Kris-Sekula/EPROM-EMU-NG/Pictures/Emulator Probe/README.MD

For DIP28 desing you can follow the YouTube video https://youtu.be/pb_EF_JVYxc

For DIP24 use the YouTube video as baseline but re-connect VCC as per desing document [Probe_Design.pdf](https://github.com/Kris-Sekula/EPROM-EMU-NG/blob/master/Probe_Design.pdf) in the main folder ... Here additonal pictures of the DIP24 probe.
