Kris-Sekula/EPROM-EMU-NG/3d-Case/Probe_lbl.PNG

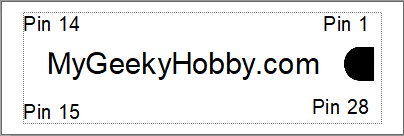
3d-Case/Probe_lbl.PNG
