Kris-Sekula/EPROM-EMU-NG/Pictures/1002_EPROM_EMU_NG_1.4.jpg

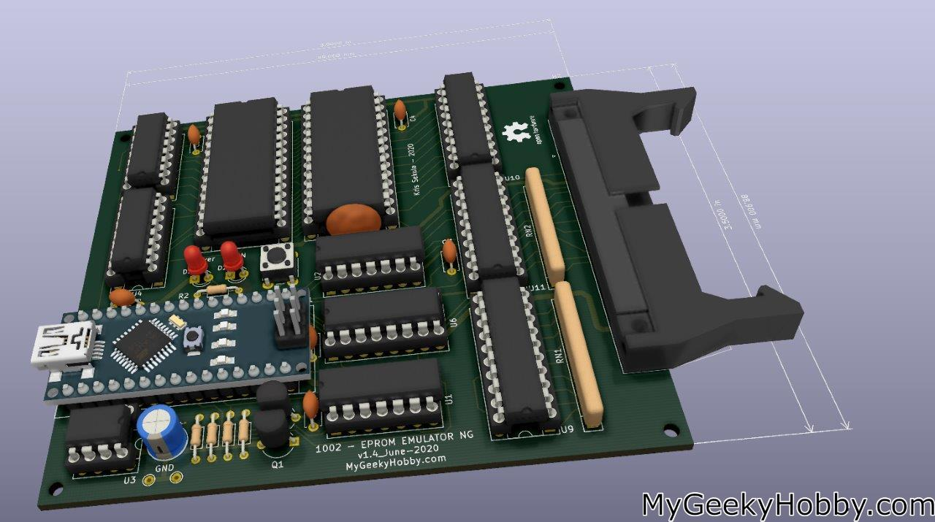
Pictures/1002_EPROM_EMU_NG_1.4.jpg
