Kris-Sekula/EPROM-EMU-NG/Pictures/EMU_1.0b_w_CA80.jpg

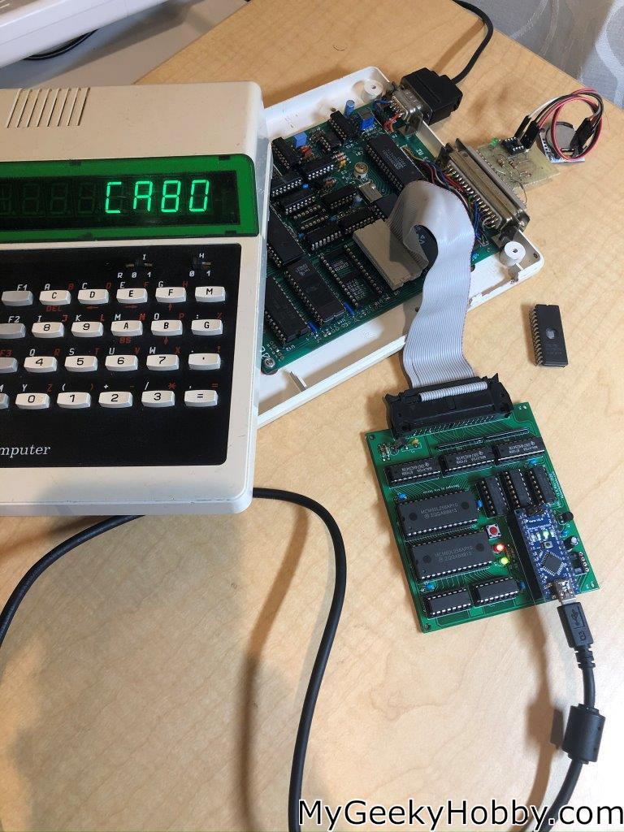
Pictures/EMU_1.0b_w_CA80.jpg
