Kris-Sekula/EPROM-EMU-NG/Pictures/EMU_1.5_ready_descr.jpg

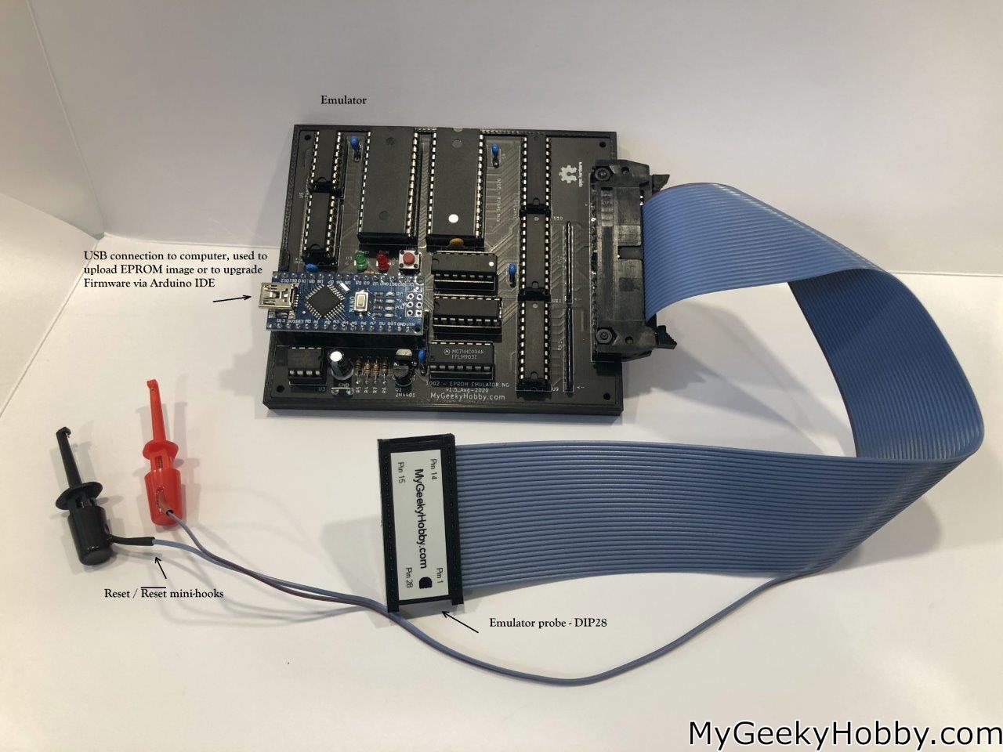
Pictures/EMU_1.5_ready_descr.jpg
