Kris-Sekula/EPROM-EMU-NG/Pictures/Emulator Probe/DIP24_1.jpg

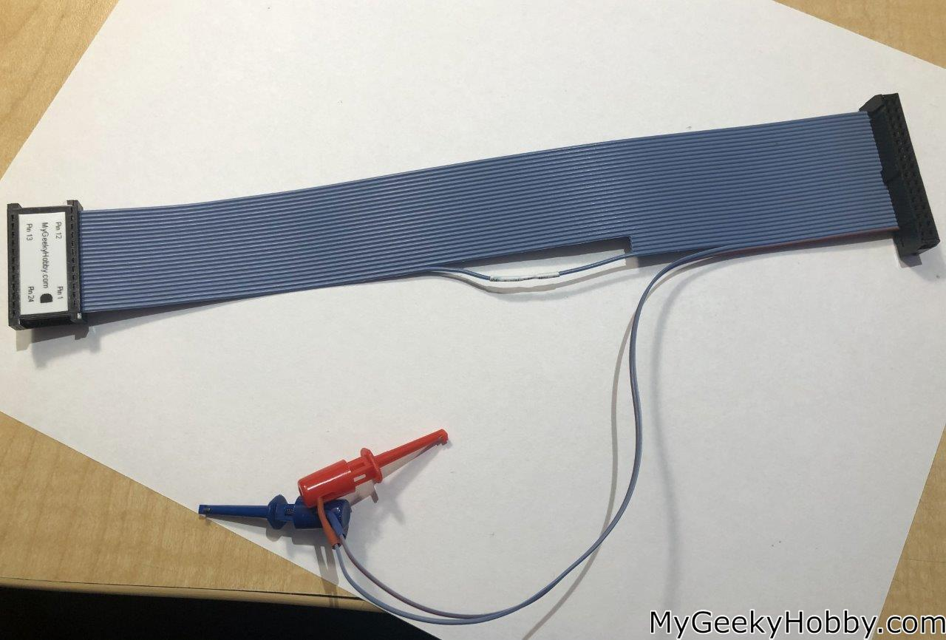
Pictures/Emulator Probe/DIP24_1.jpg
