Kris-Sekula/EPROM-EMU-NG/Pictures/Emulator Probe/DIP24_2.jpg

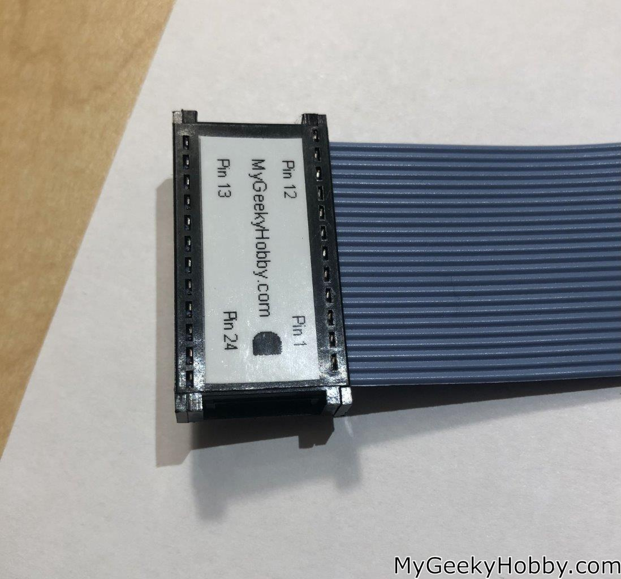
Pictures/Emulator Probe/DIP24_2.jpg
