Kris-Sekula/EPROM-EMU-NG/Pictures/Emulator Probe/DIP24_3.jpg

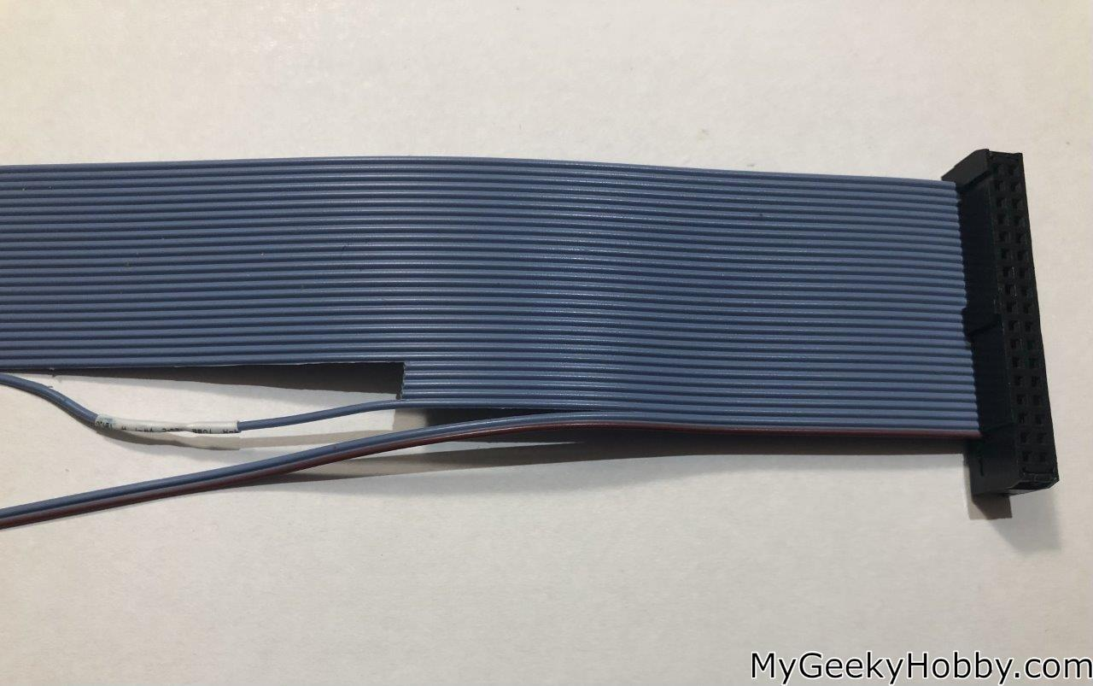
Pictures/Emulator Probe/DIP24_3.jpg
