Kris-Sekula/EPROM-EMU-NG/Pictures/Emulator Probe/DIP24_5.jpg

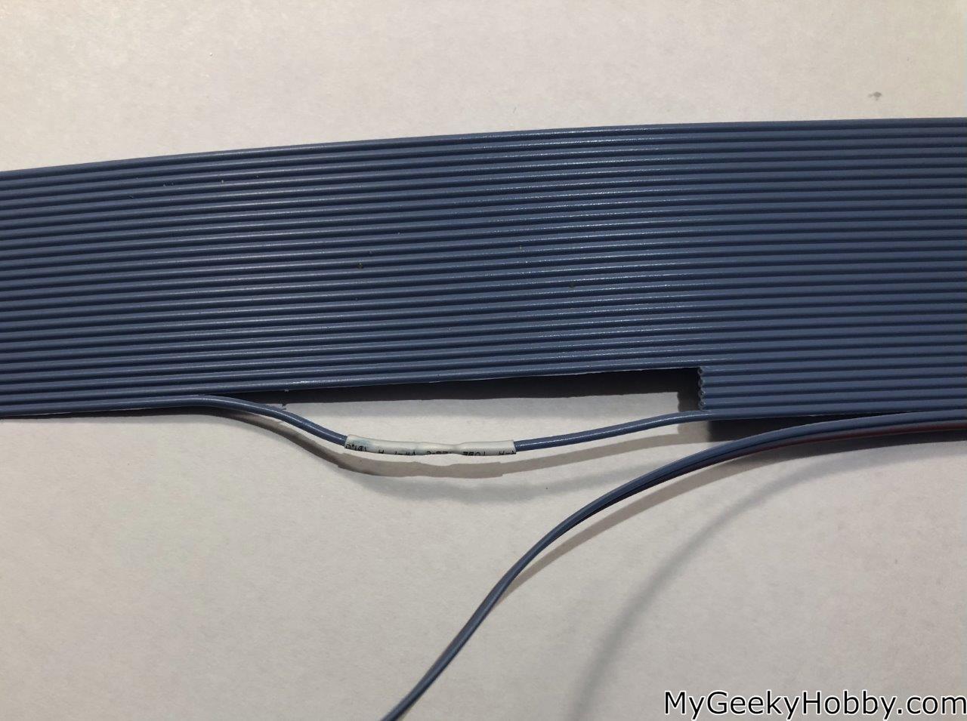
Pictures/Emulator Probe/DIP24_5.jpg
