Kris-Sekula/EPROM-EMU-NG/Pictures/EMU_1.0b_w_C64_test.jpg

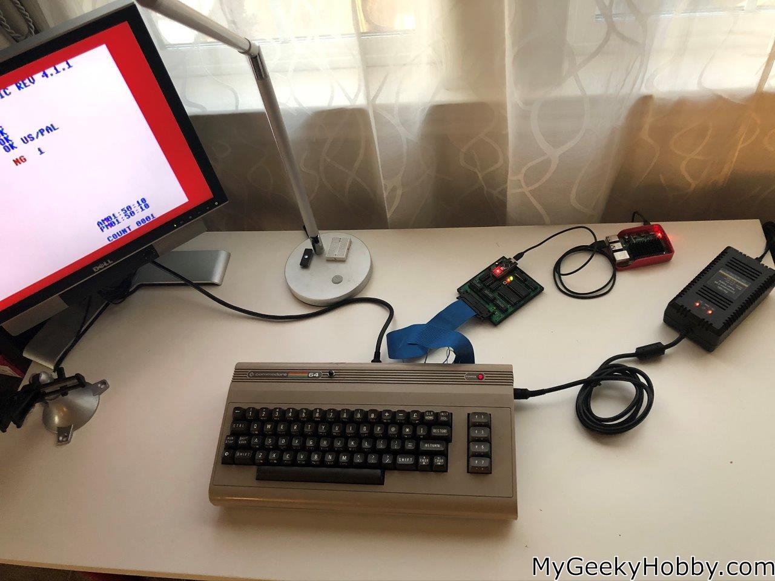
Pictures/EMU_1.0b_w_C64_test.jpg
