Kris-Sekula/EPROM-EMU-NG/1002_EPROM_EMU_NG_1.7b.pdf

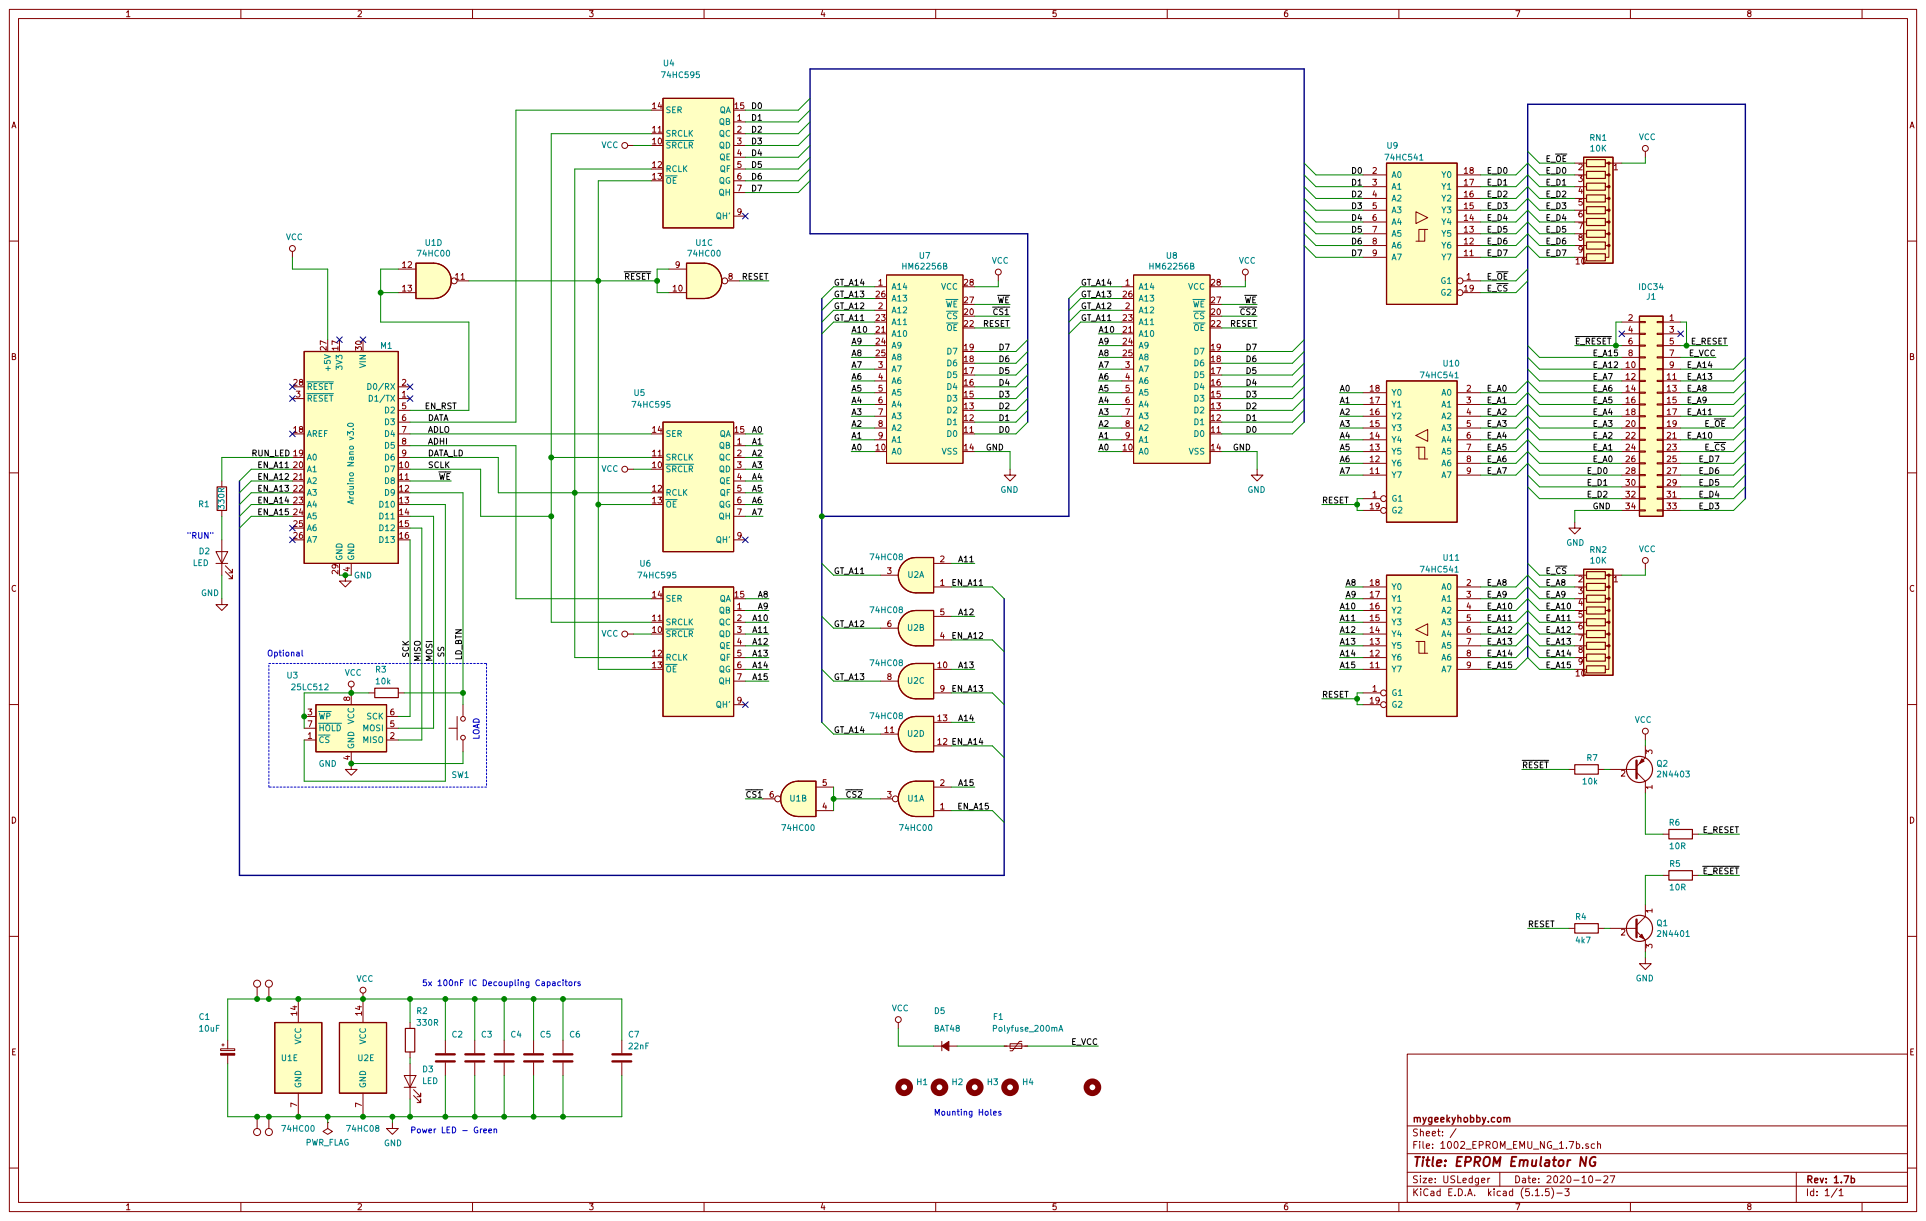
[picture p77: page 1]

Mounting Holes Power LED - Green

File: 1002_EPROM_EMU_NG_1.7b.sch Sheet: / mygeekyhobby.com

Id: 1/1 Title: EPROM Emulator NG
