Kris-Sekula/EPROM-EMU-NG/KiCad Sources/1.9/1002_EPROM_EMU_NG_1.9.pdf

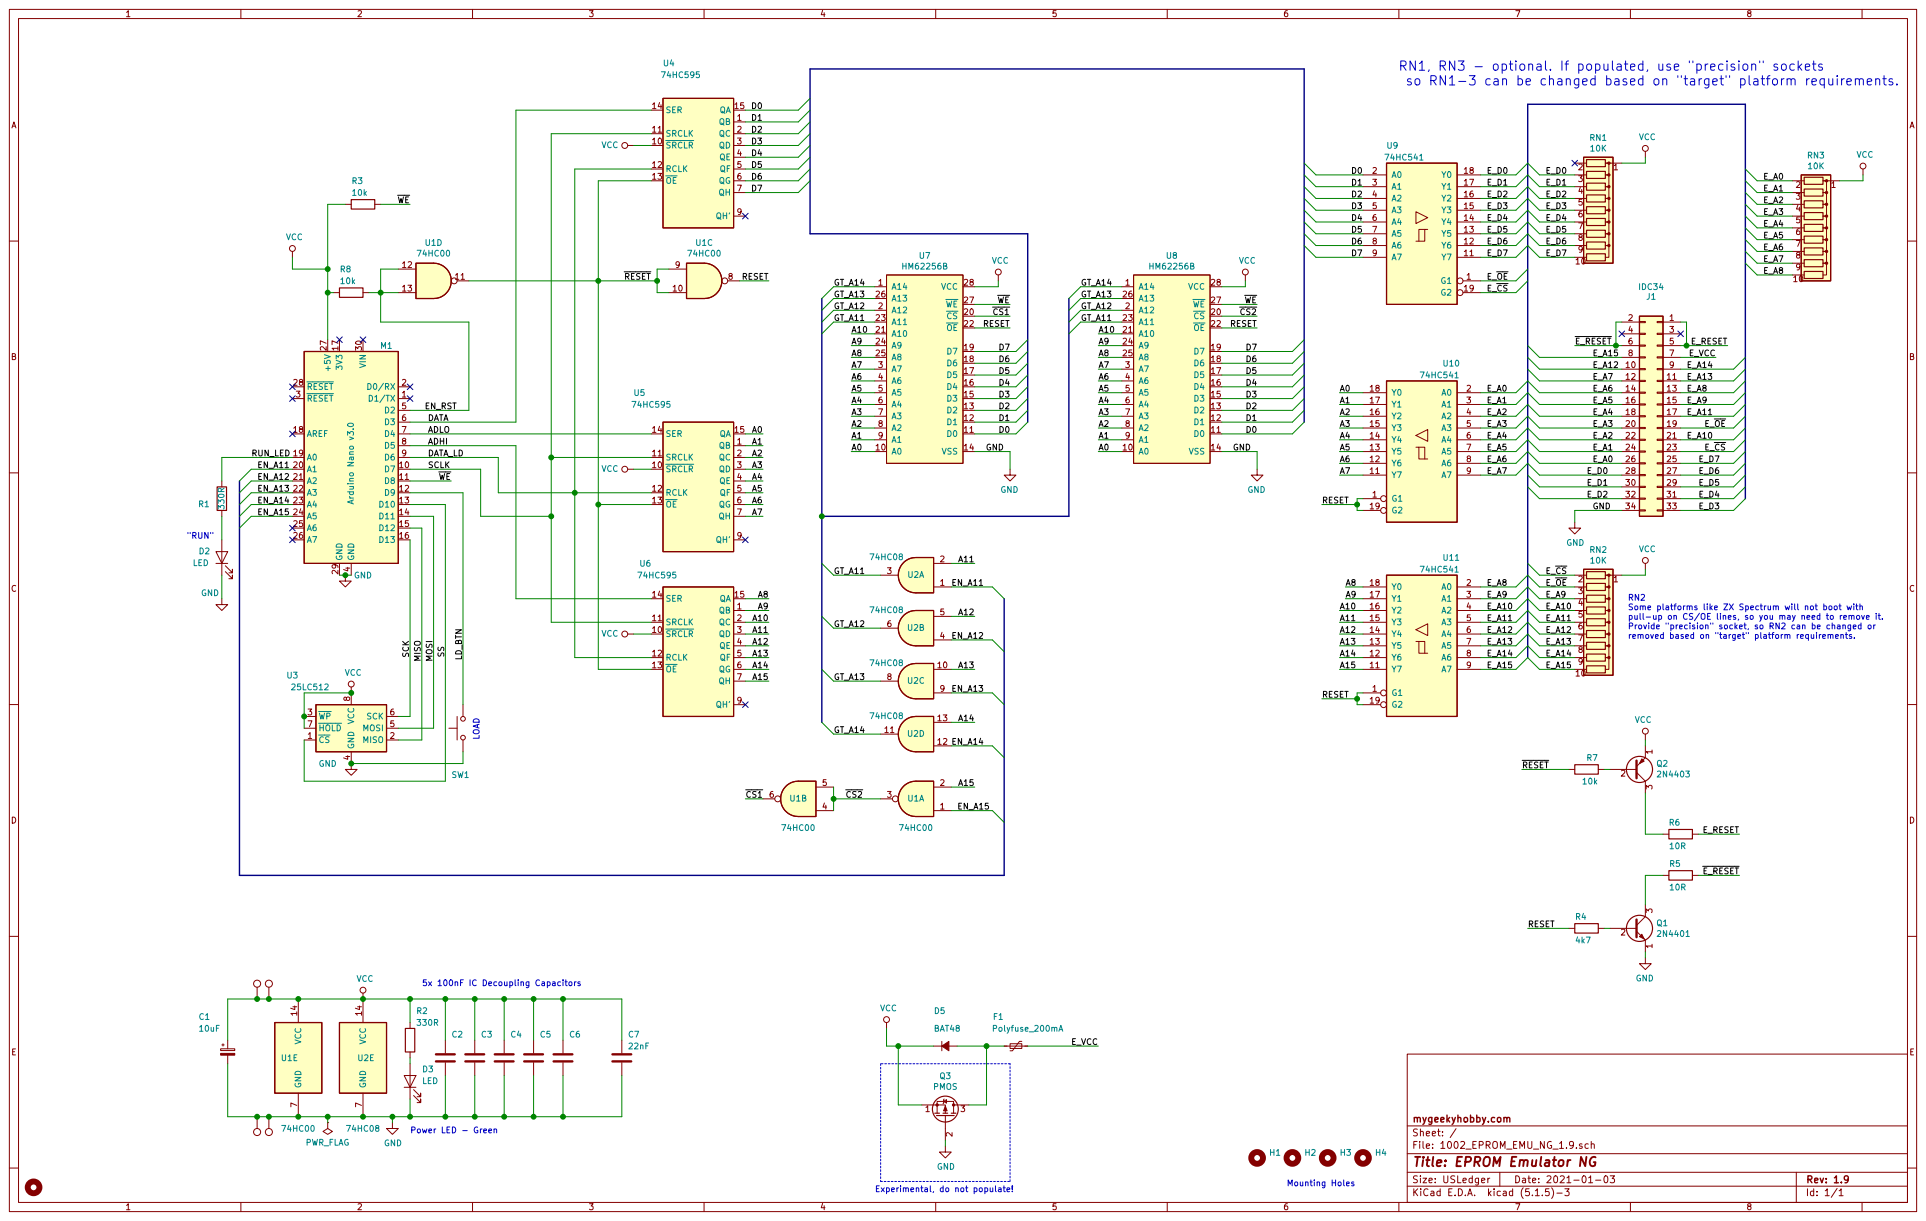
[picture p78: page 1]
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

File: 1002_EPROM_EMU_NG_1.9.sch Sheet: / mygeekyhobby.com

Id: 1/1 Title: EPROM Emulator NG

Experimental, do not populate!
