Kris-Sekula/EPROM-EMU-NG/1002_EPROM_EMU_NG.pdf

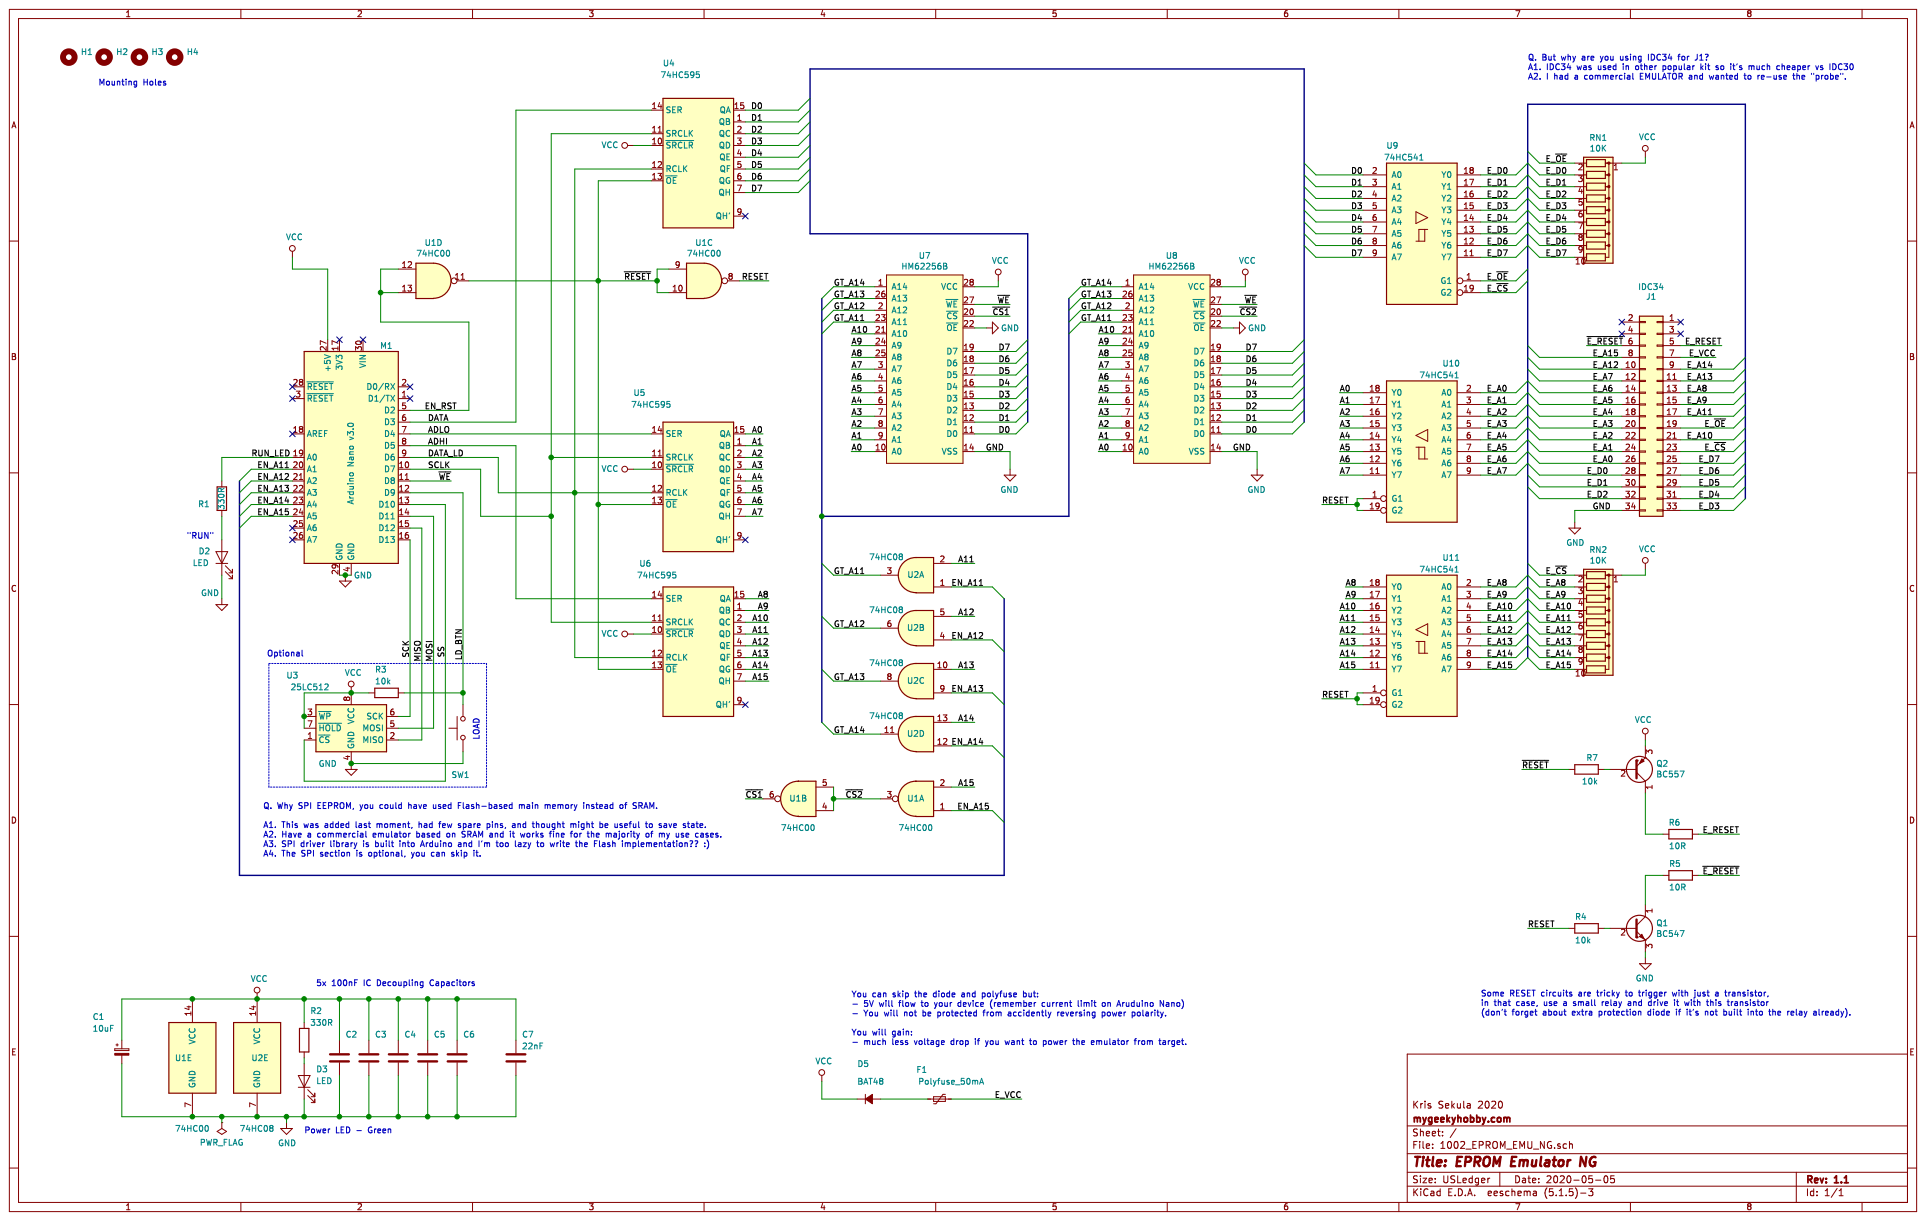
[picture p80: page 1]
